galaxyzwj/micro-radar/include/ConfigurationWebServer.h

#pragma once

#include <ESPAsyncWebServer.h>
#include <Preferences.h>

class ConfigurationWebServer {
private:
    AsyncWebServer server;
    Preferences prefs;

public:
    ConfigurationWebServer() : server(80), prefs() {}
    ConfigurationWebServer(int port) : server(port), prefs() {}

    void Initialise();
};
